daneski13/Junco/img/LED.webp

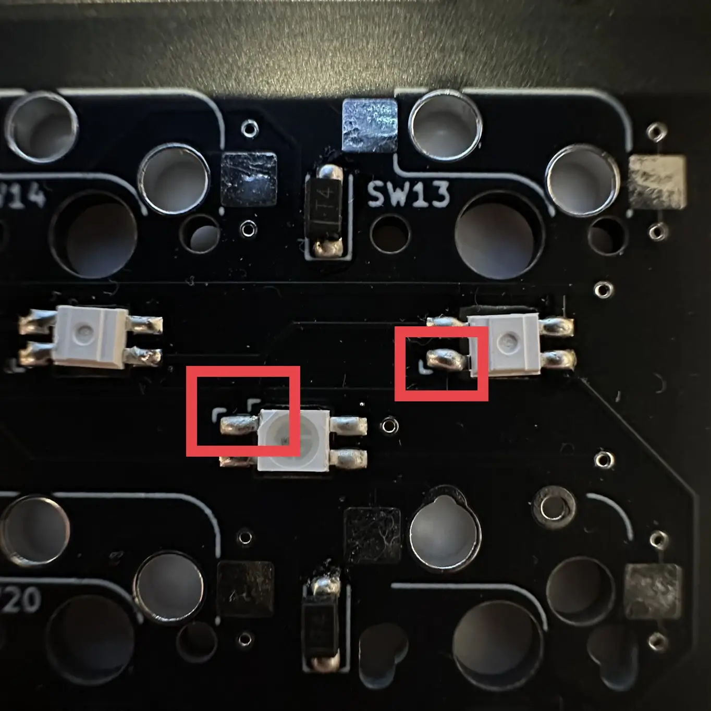
img/LED.webp
