daneski13/Junco/img/PCB 3D render.webp

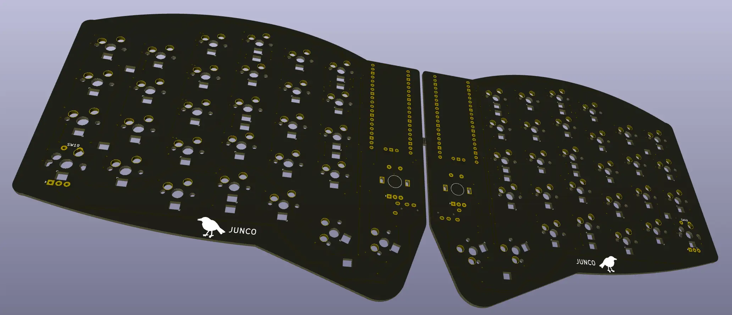
img/PCB 3D render.webp
