daneski13/Junco/img/pico_frontside.webp

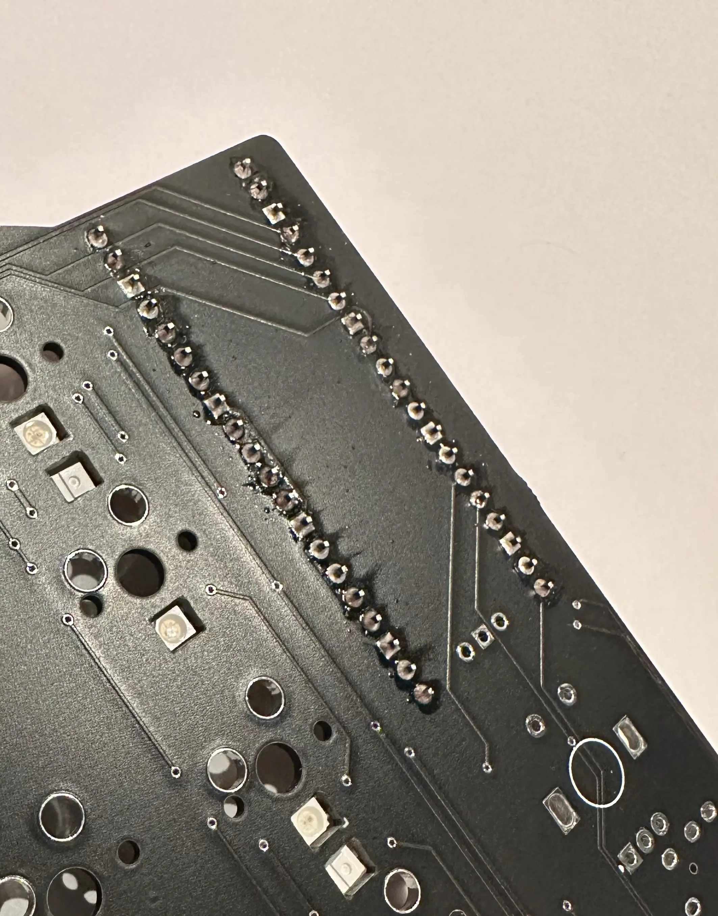
img/pico_frontside.webp
